skylar-slideshows/DigitalAnalogConsole/Analog Design/2 Design - EQ/1 State Variable Filter/state_var.asc

3n: cap; 3n
C2: cap; 3n
R1: res; 100k
R2: res; 10k
R3: res; 10k
R4: res; 10k
R5: res; 10.6k
R6: res; 10.6k
R7: res; 100k
R8: res; 10k
U1: opamp2; NE5532
U2: opamp2; NE5532
U3: opamp2; NE5532
U4: opamp2; NE5532
Vcc: voltage; 18
Vee: voltage; -18
Vin: voltage; 0; AC 1 0
Named nets: 0, IN, HP, BP, LP
.include NE5532.sub
Summing
Integrator 1
Integrator 2
Example design: BP,
PeakGain = Unity,
f_center = 5k,
BW = +/-100Hz -> -3dB
 
DESIGN: Frequency Scale
Let all R except R1, R7 = 1ohm. Let all C = 1F.
 
Av = KQ = R7/R1
=> For unity gain, set 1/k = Q (R1 = R7)
 
BW = 200Hz
=> Q = f_center / BW = 5k / 200 = 25
 
f_center = 1 / (2piRC)
=> C = 1/ (2pi * 1ohm * f_center) = 1 / 31.42k = 31.8uF
 
Z scale by 10k:
R = 10k
C = 31.8uF / 10k = 3.18nF
Q = 25 * 10k = 250k = R7 = 1/k = R1
R1 = 1/k
R7 = Q
.ac dec 100 10 100k
In reality, add bias compensation resistors to In+
